TinyCircuits/TinyCircuits-TinyShield-16_Edge_Leds-ASD2411/images/ASD2411-R-LG-Tutorial-Image-03.jpg

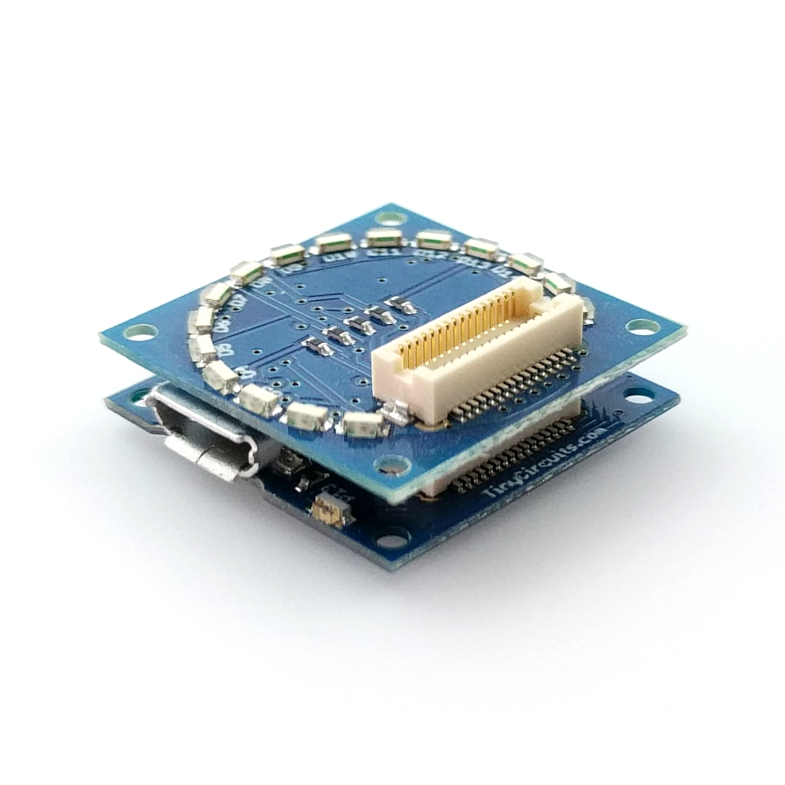
images/ASD2411-R-LG-Tutorial-Image-03.jpg
